MKMLLER/6-DOF_Robot./RA_Main/Images/Main_Images/Image1.jpg

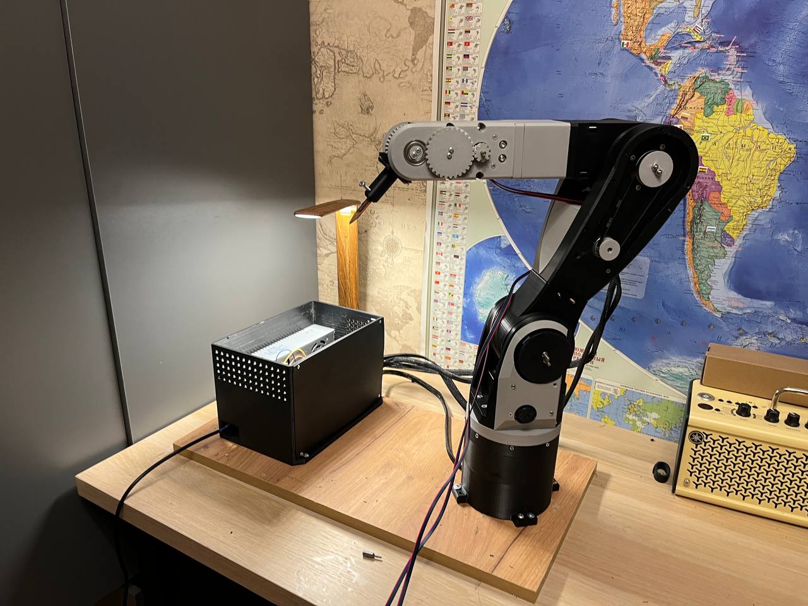
RA_Main/Images/Main_Images/Image1.jpg
