MKMLLER/6-DOF_Robot./RA_Main/Images/Main_Images/Image2.jpg

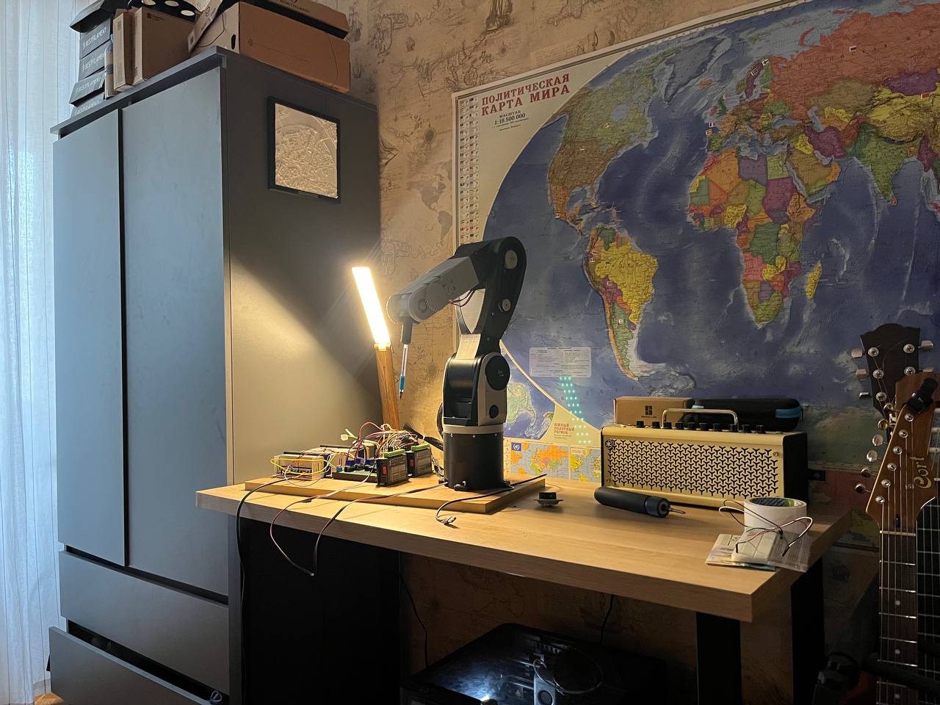
RA_Main/Images/Main_Images/Image2.jpg
