MKMLLER/6-DOF_Robot./RA_Main/Images/Main_Images/Image3.jpg

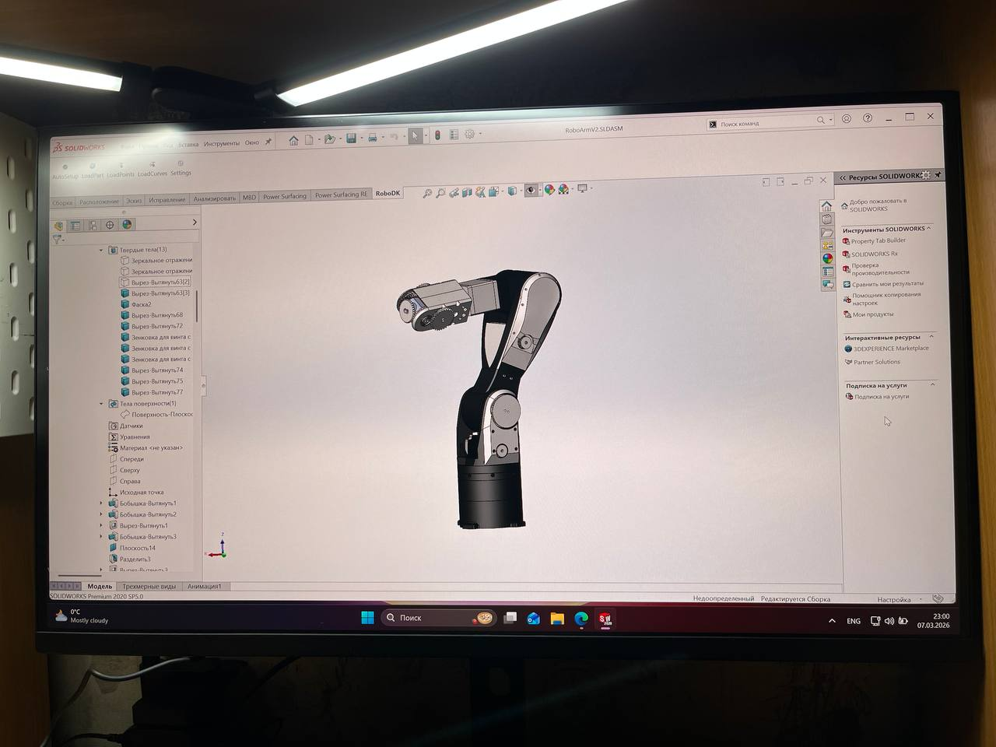
RA_Main/Images/Main_Images/Image3.jpg
